domstoppable/FoodWasteScaleAndDisplay/DisplayApp/Landfill/9.png

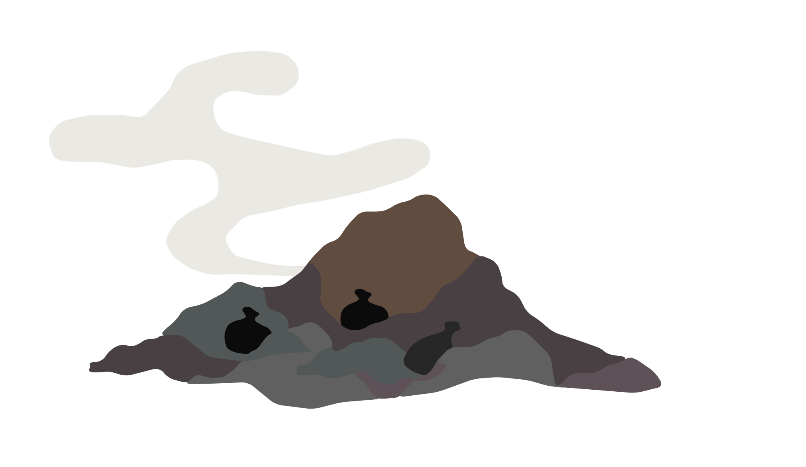
DisplayApp/Landfill/9.png
