domstoppable/FoodWasteScaleAndDisplay/DisplayApp/Landfill/Untitled.png

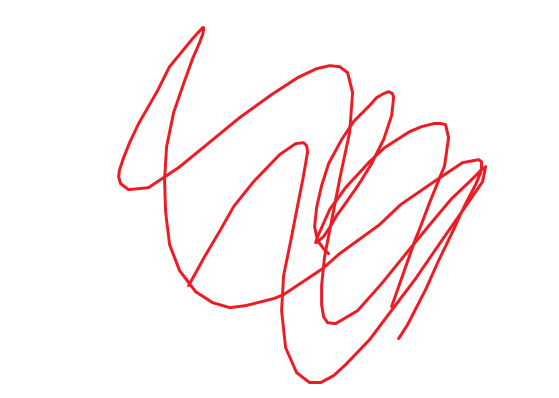
DisplayApp/Landfill/Untitled.png
